xms12138/casa0018_Zihang_He/Assessment/Projects/Final_Project/report_figures/01_data/publish version.png

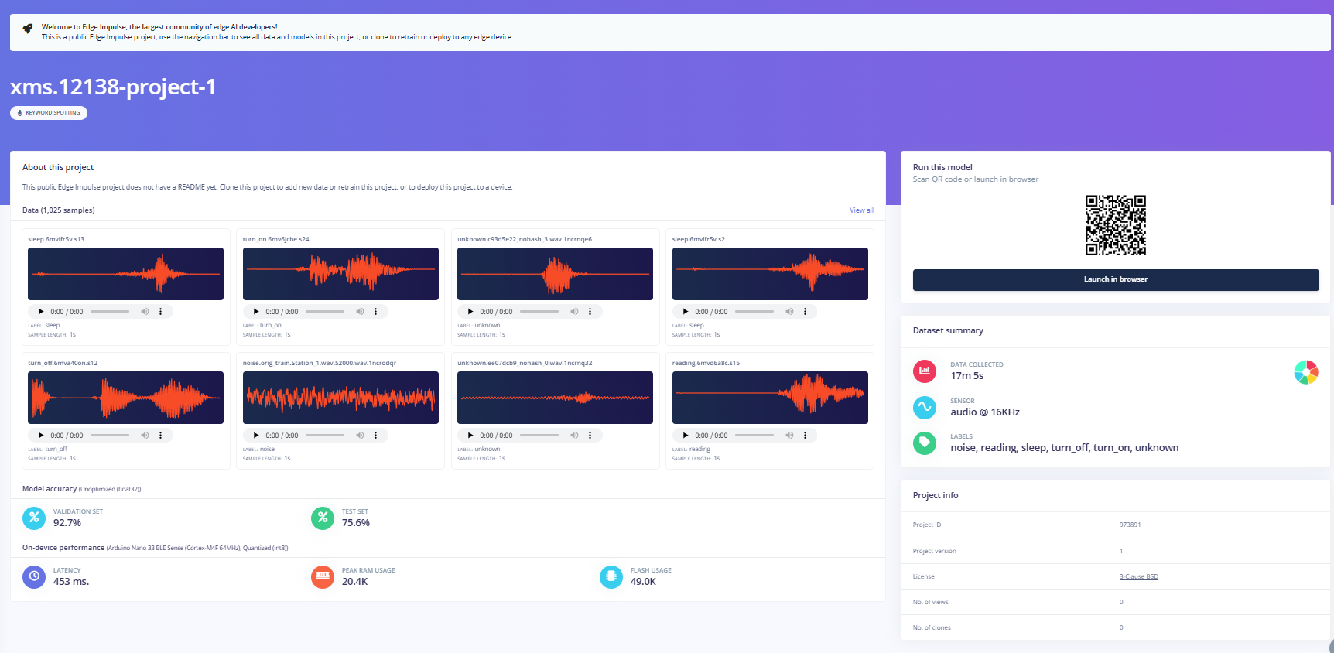
Assessment/Projects/Final_Project/report_figures/01_data/publish version.png
