xms12138/casa0018_Zihang_He/Assessment/Projects/Final_Project/report_figures/01_data/train_dataset.png

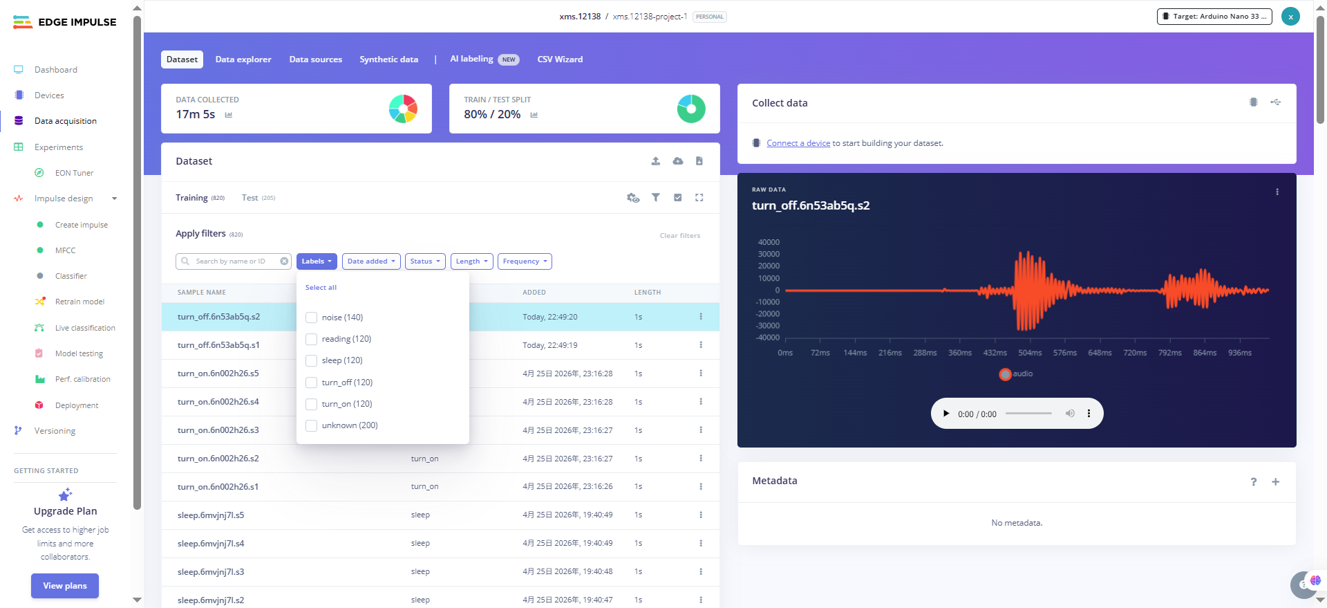
Assessment/Projects/Final_Project/report_figures/01_data/train_dataset.png
