xms12138/casa0018_Zihang_He/Assessment/Projects/Final_Project/report_figures/01_data/turn_off.png

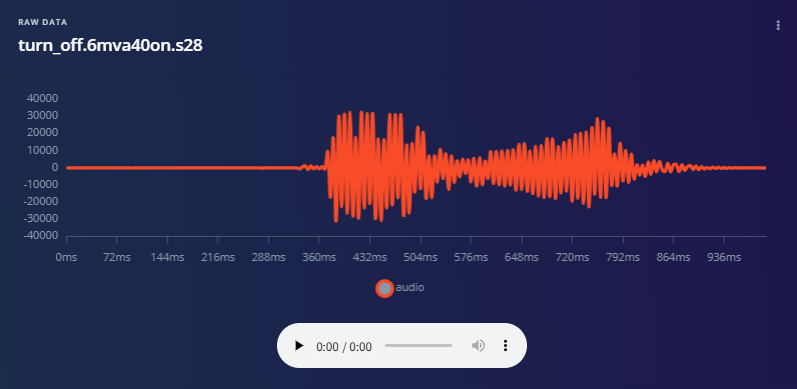
Assessment/Projects/Final_Project/report_figures/01_data/turn_off.png
