xms12138/casa0018_Zihang_He/Assessment/Projects/Final_Project/report_figures/02_methods/mfcc_autotune_default.png

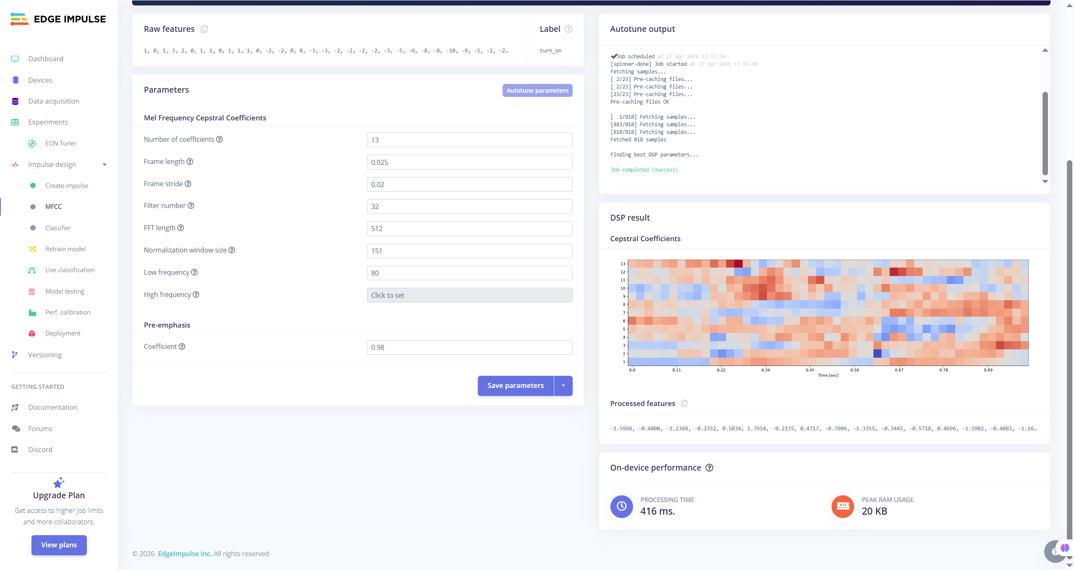
Assessment/Projects/Final_Project/report_figures/02_methods/mfcc_autotune_default.png
