xms12138/casa0018_Zihang_He/Assessment/Projects/Final_Project/report_figures/05_hardware/interior.jpg

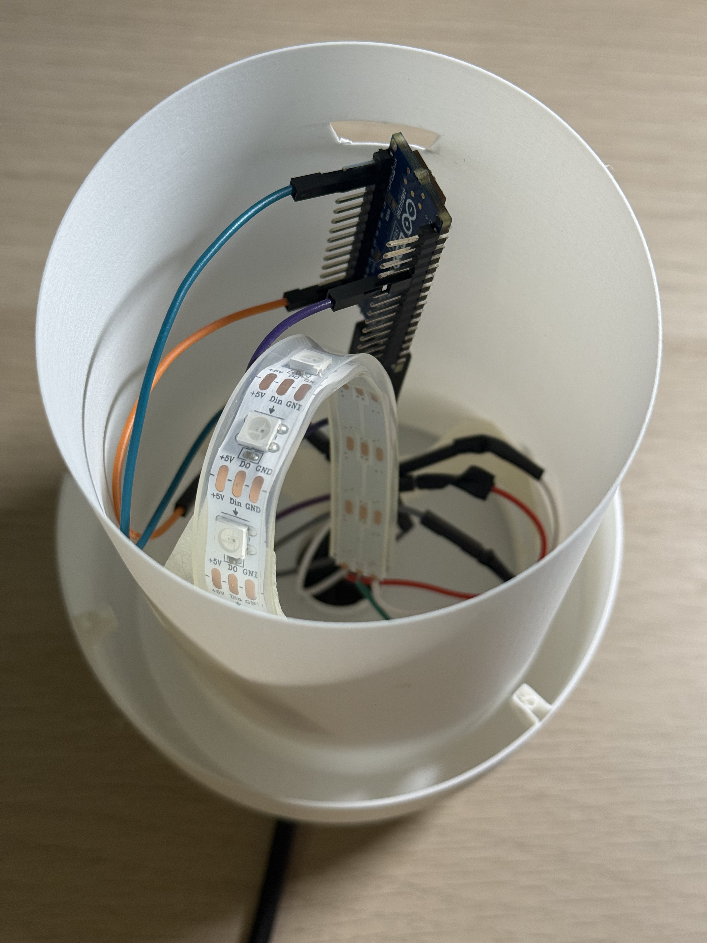
Assessment/Projects/Final_Project/report_figures/05_hardware/interior.jpg
