xms12138/casa0018_Zihang_He/Assessment/Projects/Final_Project/report_figures/05_hardware/light.jpg

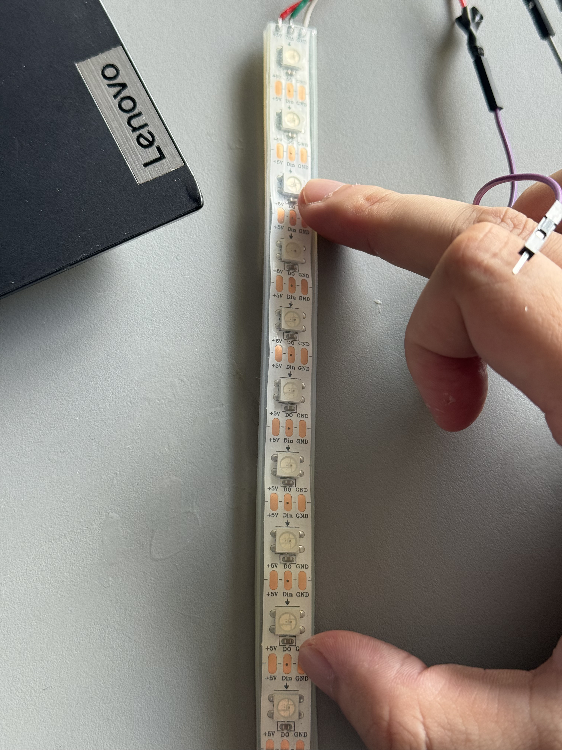
Assessment/Projects/Final_Project/report_figures/05_hardware/light.jpg
