xms12138/casa0018_Zihang_He/Assessment/Projects/Final_Project/report_figures/03_experiments/exp_dense/dense_test_float32.png

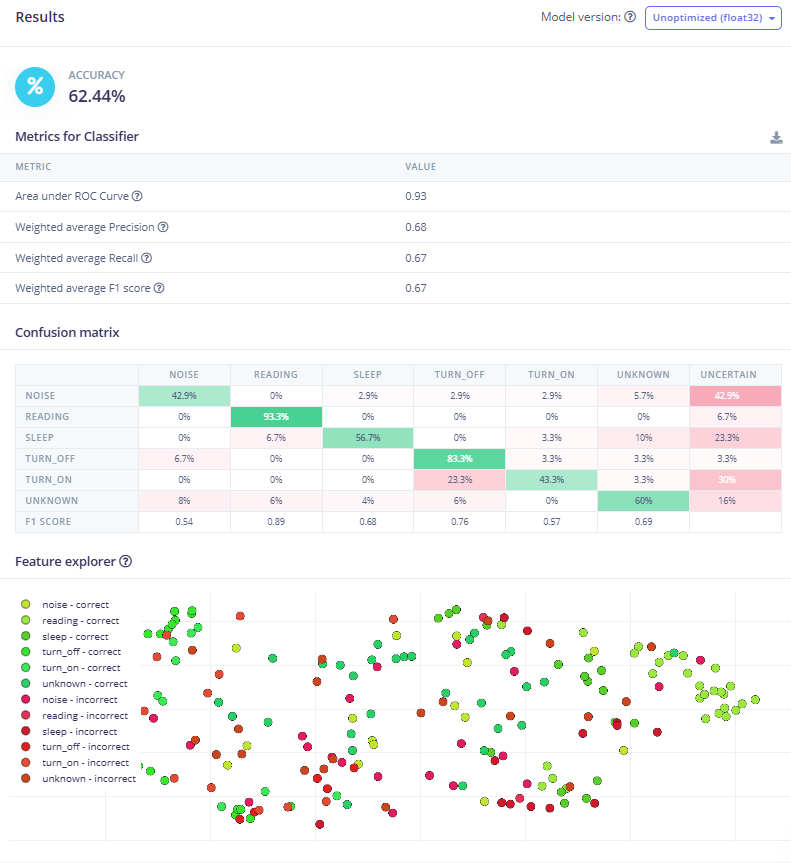
Assessment/Projects/Final_Project/report_figures/03_experiments/exp_dense/dense_test_float32.png
