xms12138/casa0018_Zihang_He/Assessment/Projects/Final_Project/report_figures/03_experiments/exp_wider/wider_test_int8.png

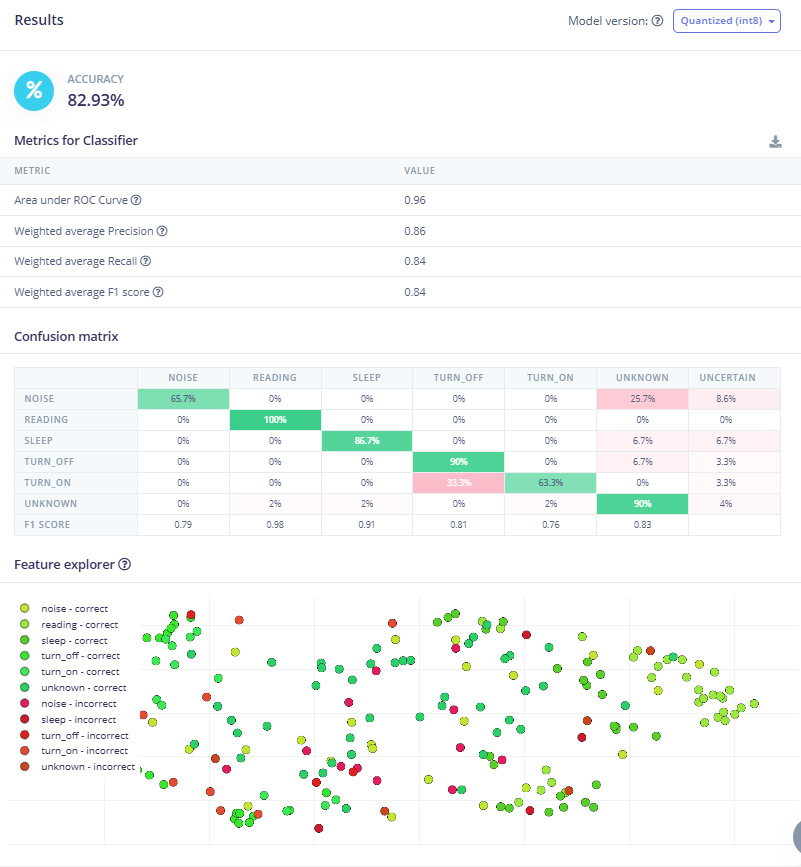
Assessment/Projects/Final_Project/report_figures/03_experiments/exp_wider/wider_test_int8.png
